KaiRoy/Chain-Measurement-Sensor/Code/Block Test Code/can_receiver.ino

#include <SPI.h>
#include "mcp_can.h"
/* Set UNO borad as receiver*/

const int spiCSPin = 10;

MCP_CAN CAN(spiCSPin);

void setup()
{
    Serial.begin(9600);

    while (CAN_OK != CAN.begin(CAN_500KBPS))
    {
        Serial.println("CAN BUS Init Failed");
        delay(500);
    }
    Serial.println("CAN BUS  Init OK!");
}


void loop()
{
    unsigned char len = 0;
    unsigned char buf[2];

    if(CAN_MSGAVAIL == CAN.checkReceive())
    {
        CAN.readMsgBuf(&len, buf);

        unsigned long canId = CAN.getCanId();

        Serial.println("-----------------------------");
        Serial.print("Group number: 0x");
        Serial.println(canId, HEX);

        for(int i = 0; i<len; i++)
        {
            Serial.print(buf[i]);
            Serial.print("\t");
        }
        Serial.println();
    }
}
